green-ecolution/Soil-Moisture-Sensor-Node/Documentation/Images/heat_inserts_adapter.jpg

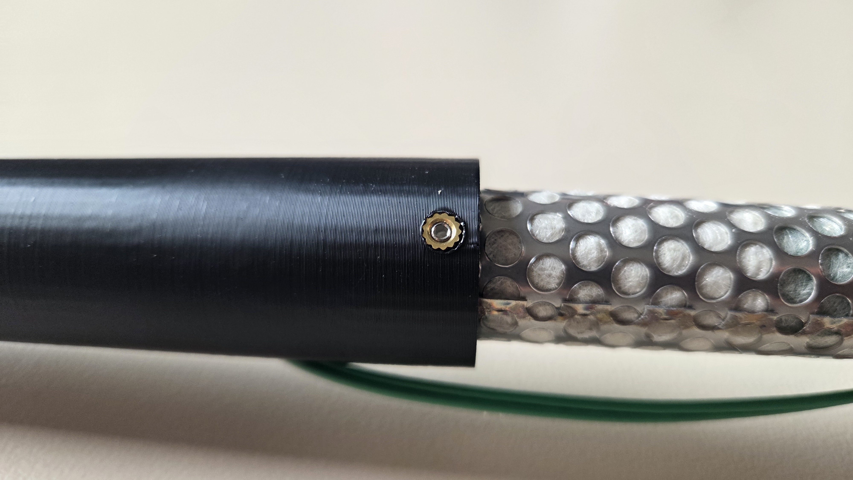
Documentation/Images/heat_inserts_adapter.jpg
